atomic14/supersise-seven-segment/firmware/src/Digits.cpp

#include "Digits.h"
#include "Digit.h"

Digits::Digits(int number_digits)
{
    m_number_digits = number_digits;
    m_digits = new Digit[number_digits];
}

Digits::~Digits()
{
    delete[] m_digits;
}

int Digits::get_digit_segment(int digit, int segment)
{
    if (digit >= 0 && digit < m_number_digits && segment >= 0 && segment <= 7)
    {
        return m_digits[digit].get_segment(segment);
    };
    return 0;
}

void Digits::set_digit(int digit, int value)
{
    if (digit >= 0 && digit < m_number_digits && value >= 0 && value <= 9)
    {
        m_digits[digit].set(value);
    }
}
